grigon/AirMonitor/case/IMG_4827-1.JPEG

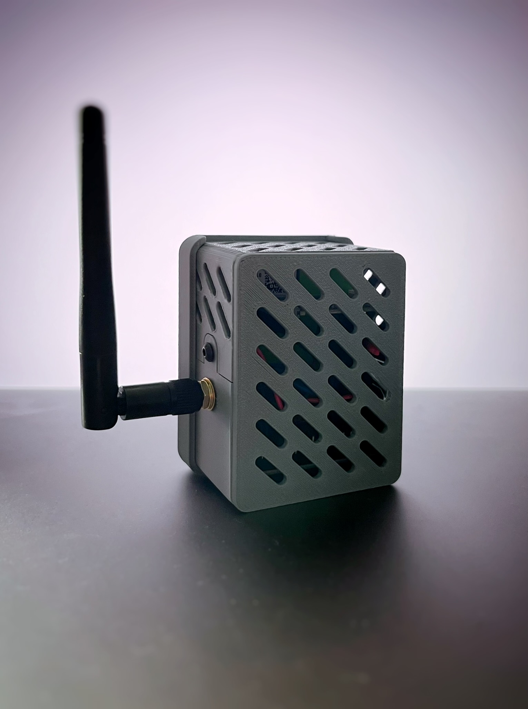
case/IMG_4827-1.JPEG
